Protocentral/ProtoCentral-ESP8266-WiFi-shield/Firmware/Screenshot/baudrate.jpg

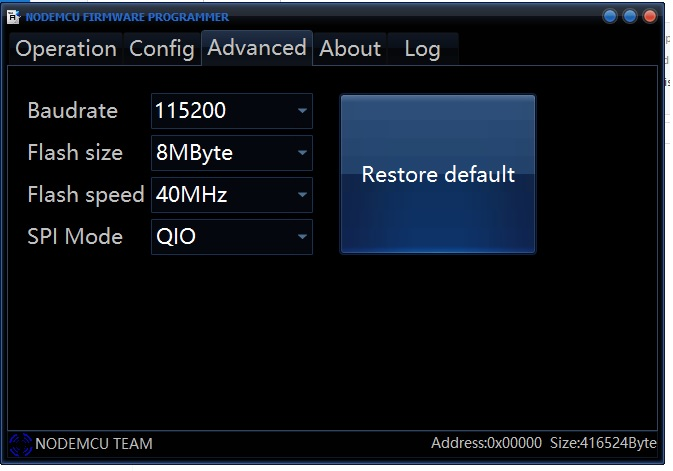
Firmware/Screenshot/baudrate.jpg
