Protocentral/ProtoCentral-ESP8266-WiFi-shield/Firmware/Screenshot/ComPort_Selection.jpg

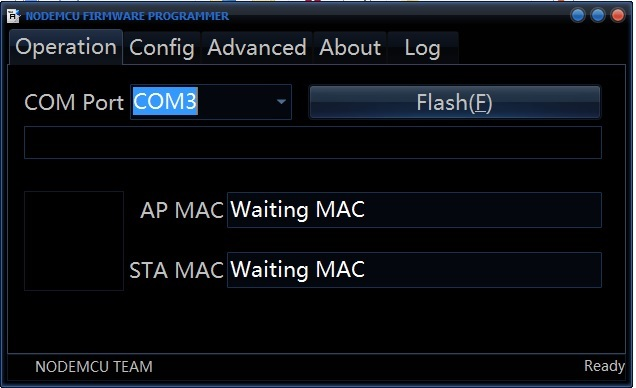
Firmware/Screenshot/ComPort_Selection.jpg
