Protocentral/ProtoCentral-ESP8266-WiFi-shield/Firmware/Screenshot/Config.jpg

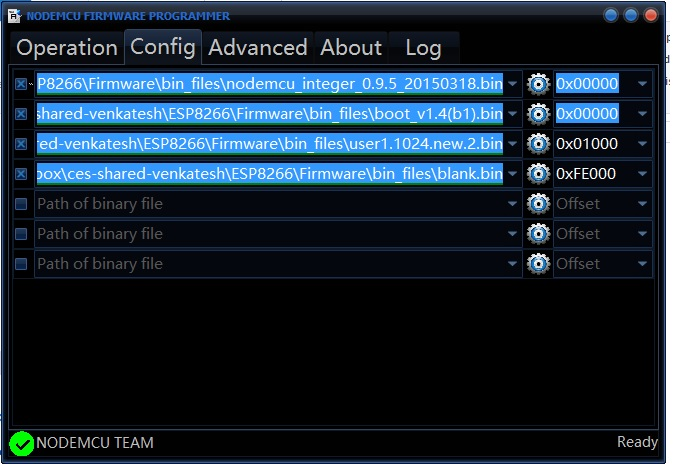
Firmware/Screenshot/Config.jpg
