Protocentral/ProtoCentral-ESP8266-WiFi-shield/Firmware/Screenshot/flashing.jpg

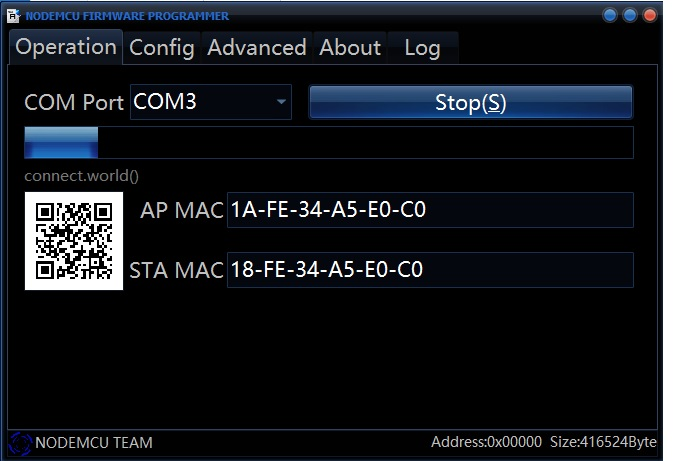
Firmware/Screenshot/flashing.jpg
